zerneo85/HASS-Animated-RocketLaunch-Lamp/Media/Rocket-Command-Node Box Back.png

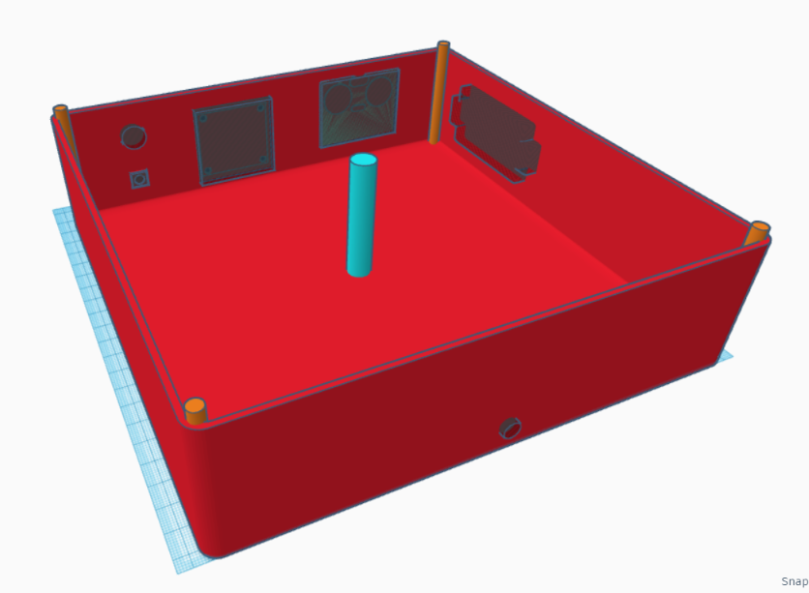
Media/Rocket-Command-Node Box Back.png
