zerneo85/HASS-Animated-RocketLaunch-Lamp/Media/Rocket-Command-Node Exhaust Fume.png

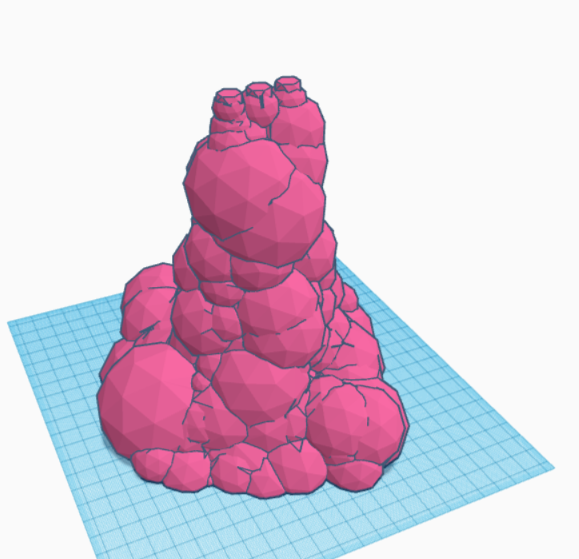
Media/Rocket-Command-Node Exhaust Fume.png
