zerneo85/HASS-Animated-RocketLaunch-Lamp/Media/Rocket-Command-Node ISD1820 ESP 38 Pin.png

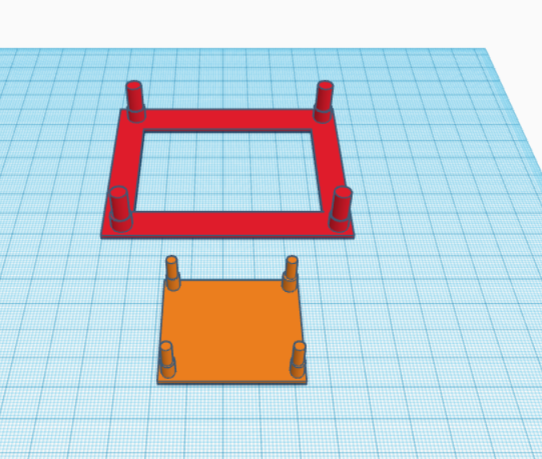
Media/Rocket-Command-Node ISD1820 ESP 38 Pin.png
