zerneo85/HASS-Animated-RocketLaunch-Lamp/Media/Rocket-Command-Node Lid.png

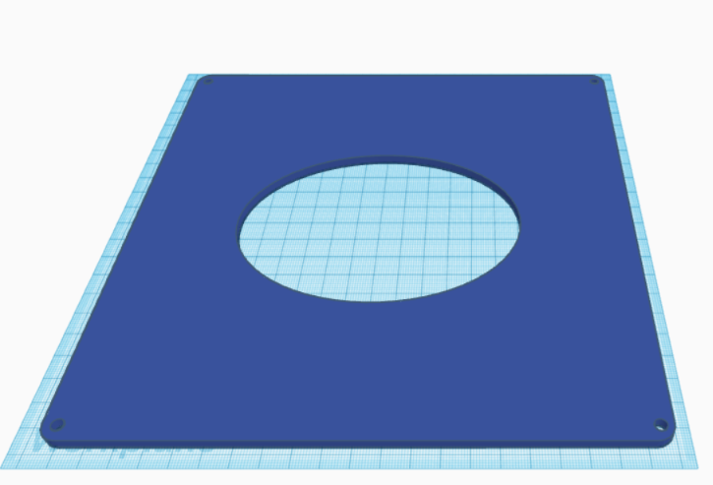
Media/Rocket-Command-Node Lid.png
